NextMicon/NextMiconCherry/boards/grape/board/board.pdf

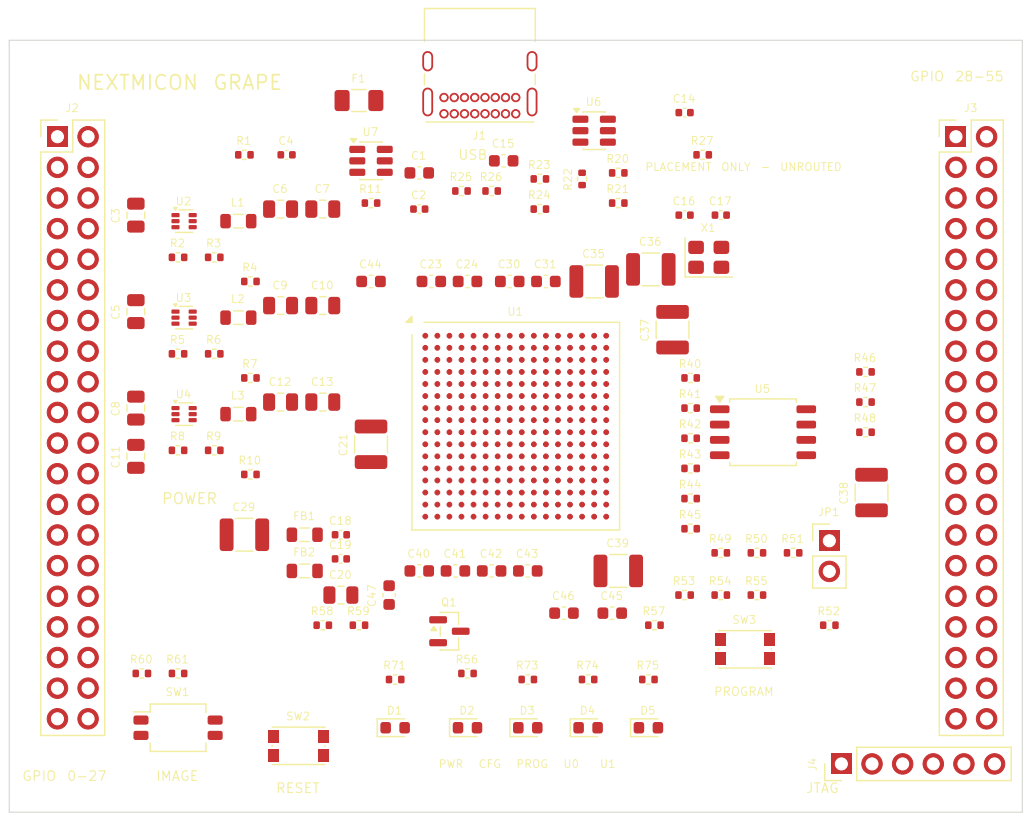
[picture p10: page 1]

GPIO 28-55 POWER NEXTMICON GRAPE
PLACEMENT ONLY - UNROUTED PROGRAM
