NextMicon/NextMiconCherry/boards/grape/board/board-back.pdf

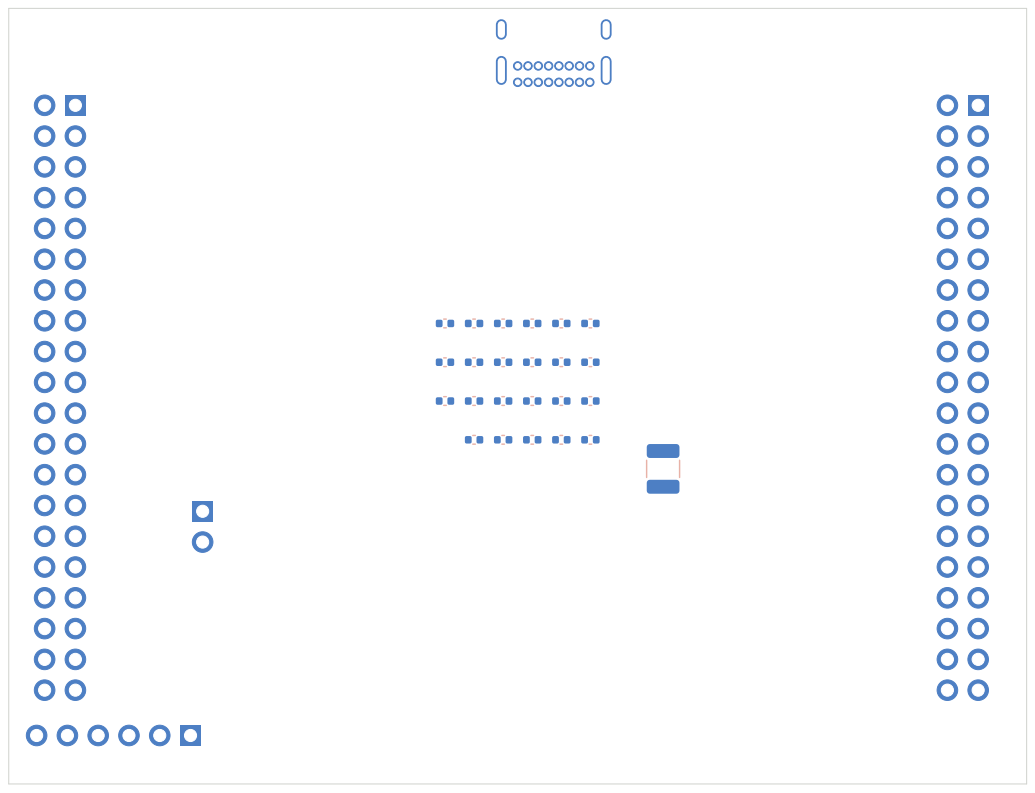
[picture p21: page 1]
